Bambleweeny57/zxspectrum_issue3b/case/Spectrum stripes files/images/rainbowsticker_blue.png

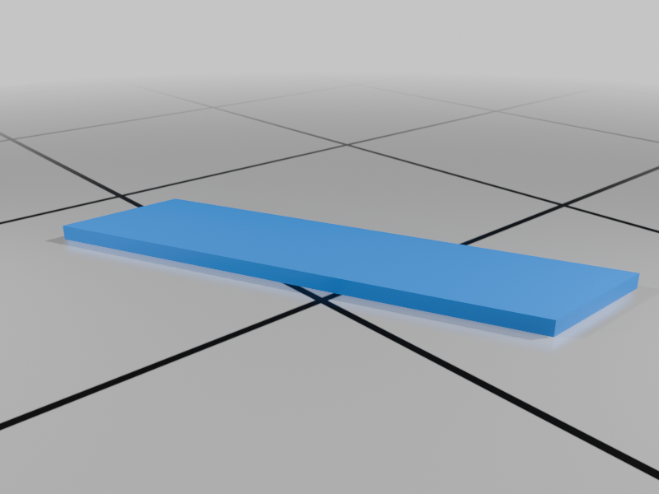
case/Spectrum stripes files/images/rainbowsticker_blue.png
